BoomBoxRobotics/Anubis/Daughterboard/x5fusion.png

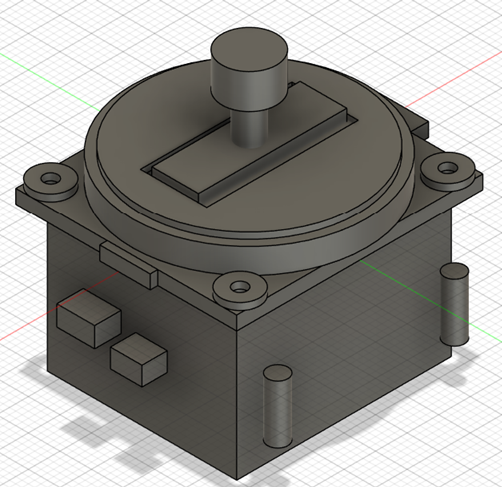
Daughterboard/x5fusion.png
