BoomBoxRobotics/Anubis/Daughterboard/fetoptions.bmp

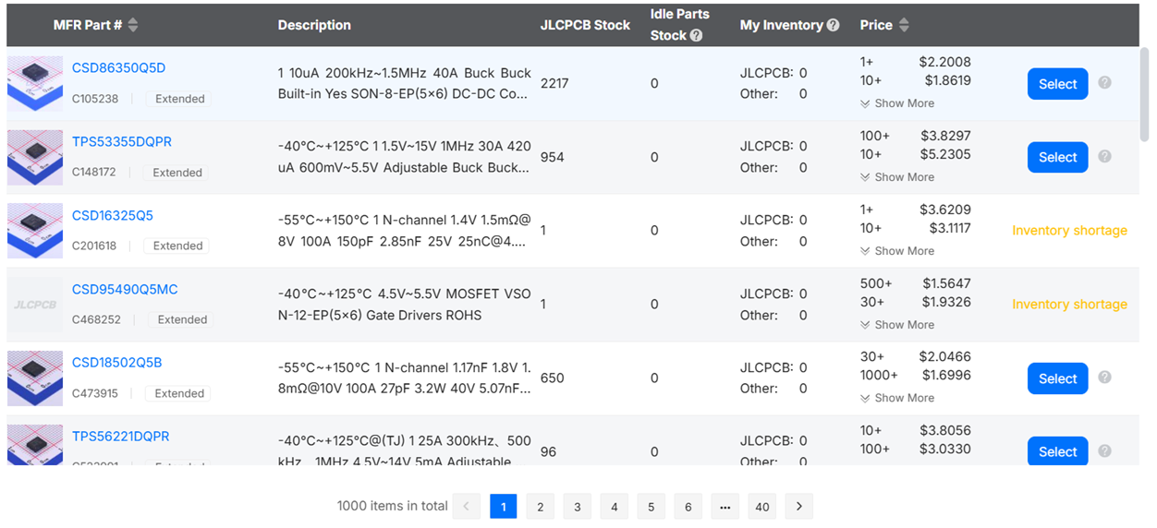
Daughterboard/fetoptions.bmp
