BoomBoxRobotics/Anubis/Daughterboard/U2.bmp

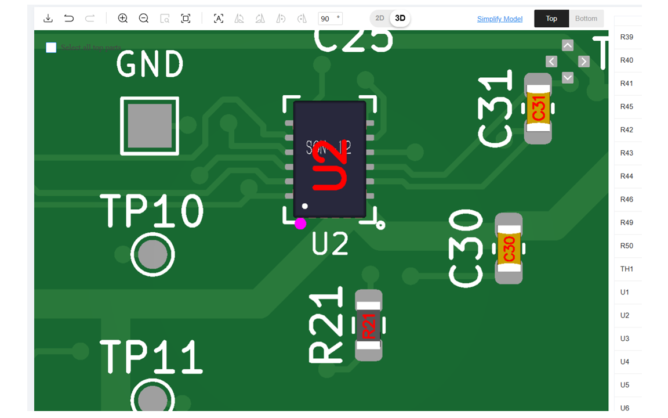
Daughterboard/U2.bmp
