BoomBoxRobotics/Anubis/Daughterboard/x5dimensions.webp

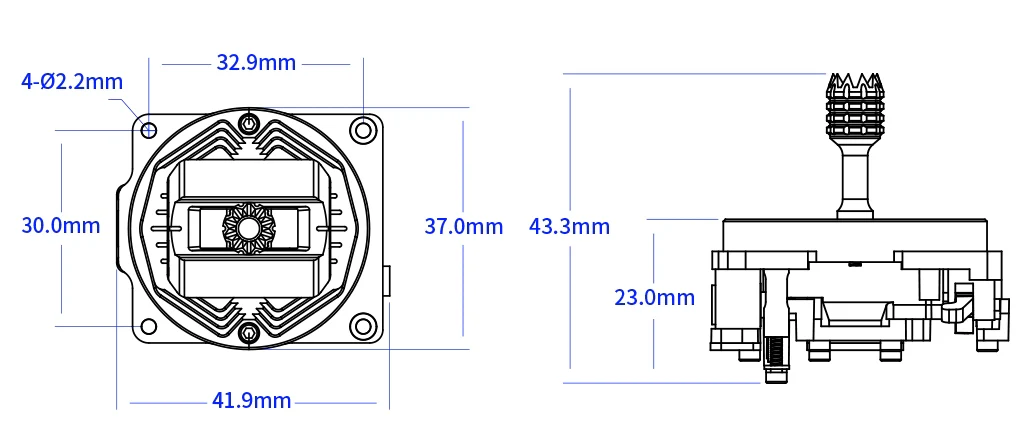
Daughterboard/x5dimensions.webp
