BoomBoxRobotics/Anubis/Daughterboard/x5Side1.webp

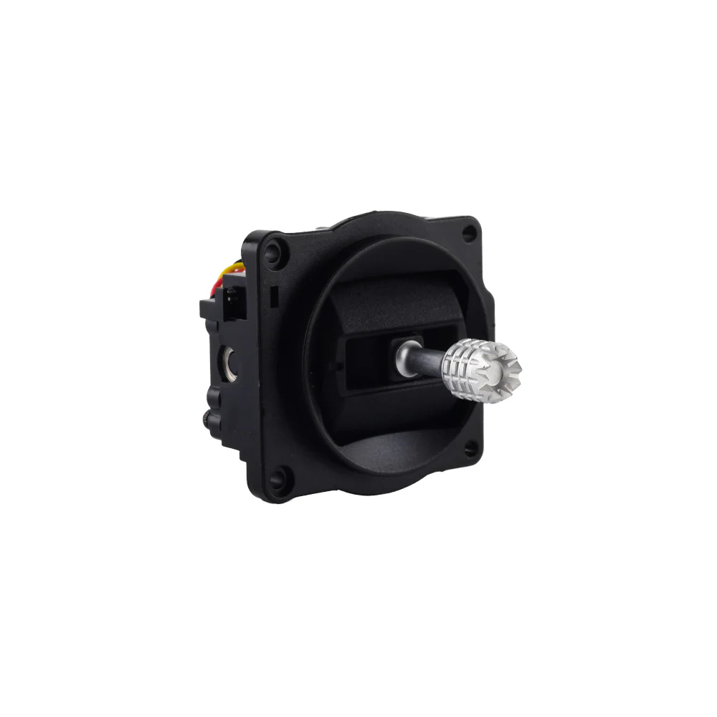
Daughterboard/x5Side1.webp
