BoomBoxRobotics/Anubis/Daughterboard/x5Side3.jpg

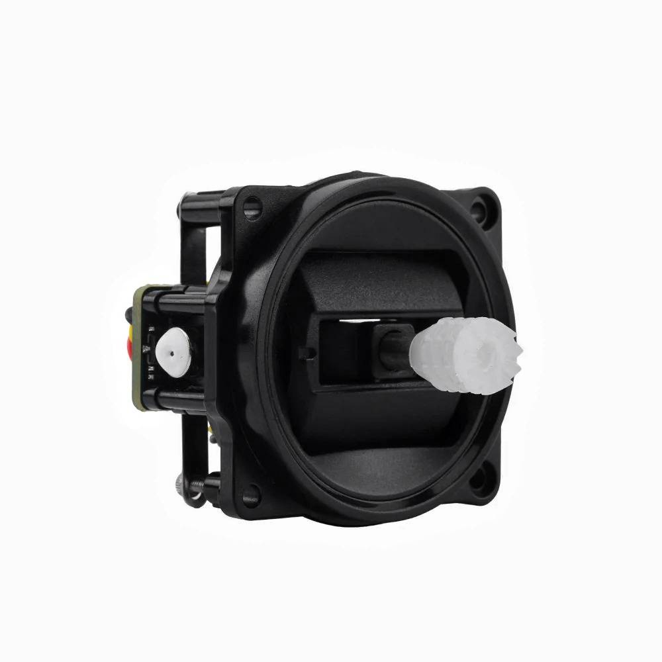
Daughterboard/x5Side3.jpg
