BoomBoxRobotics/Anubis/Hosyond_apr24b/Daughterboard/Daughterboard_pinlevel_preview.png

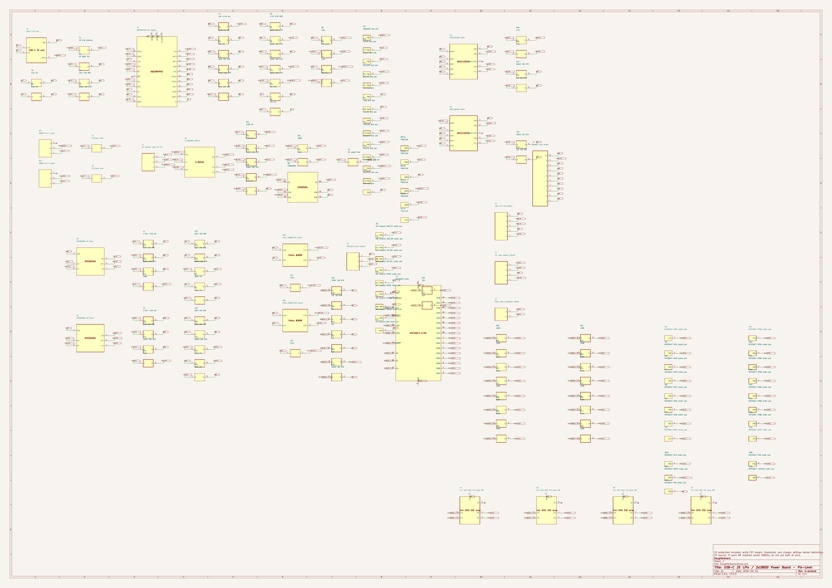
Hosyond_apr24b/Daughterboard/Daughterboard_pinlevel_preview.png
