BoomBoxRobotics/Anubis/Hosyond_apr24b/Games/Dungeon_Run_Pickups.png

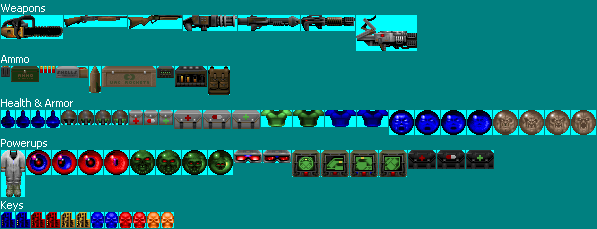
Hosyond_apr24b/Games/Dungeon_Run_Pickups.png
