BoomBoxRobotics/Anubis/Hosyond_apr24b/Games/Dungeon_Run_Text.png

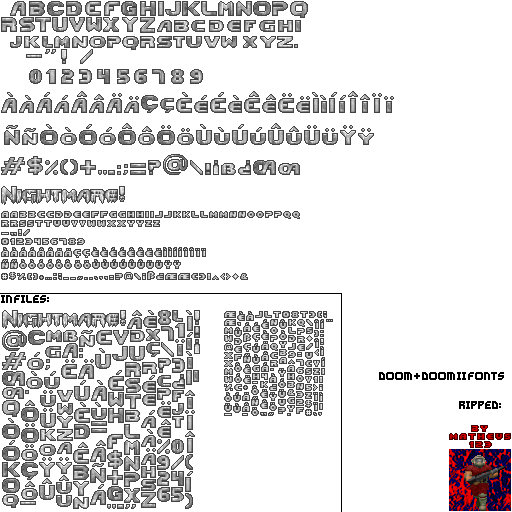
Hosyond_apr24b/Games/Dungeon_Run_Text.png
