BoomBoxRobotics/Anubis/Hosyond_apr24b/Games/Dungeon_Run_Weapons.png

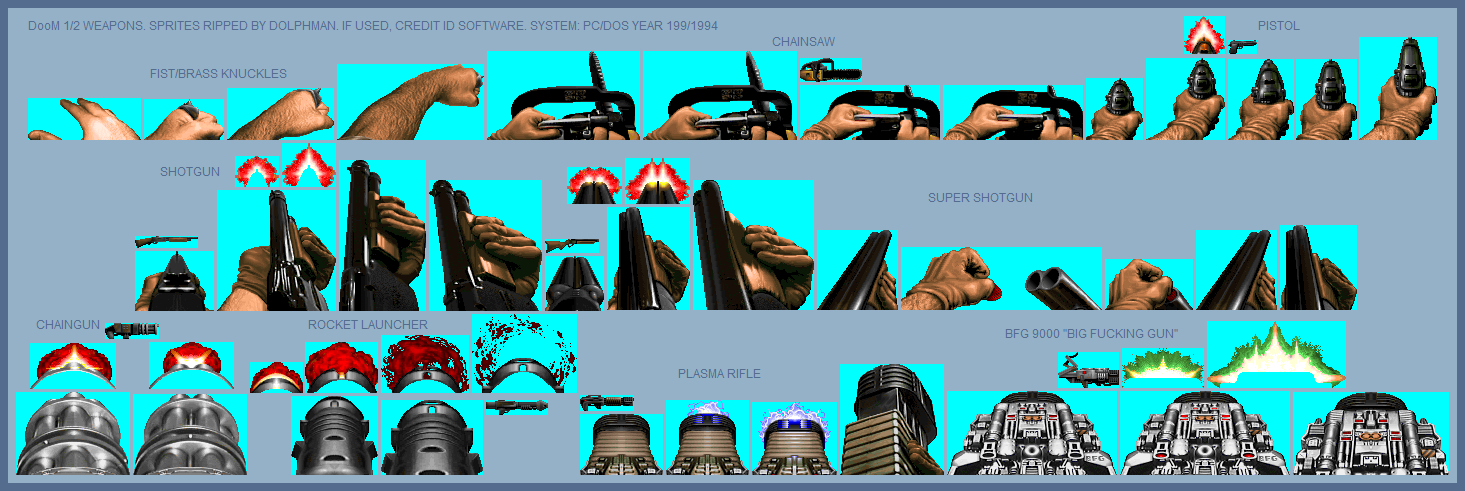
Hosyond_apr24b/Games/Dungeon_Run_Weapons.png
