BoomBoxRobotics/Anubis/Hosyond_apr24b/Daughterboard/Daughterboard_architecture_bom.csv

Refs | Value | Footprint | Qty | DNP
A1 | Fuse + VBUS TVS + CIN |  | 1
A2 | BQ2970 + dual NFET |  | 1
BT1 | 2x 18650 1S2P |  | 1
J1 | USB-C 5V Sink |  | 1
J2 | Power outputs |  | 1
J3 | Hosyond ESP32-S3 GPIO |  | 1
SW1 | Pololu #2808 5V switch |  | 1
SW2 | Pololu #2808 3V3 switch |  | 1
U1 | BQ24074RGT |  | 1
U3 | TPS61023 5V |  | 1
U4 | TPS63031 3V3 |  | 1
