BoomBoxRobotics/Anubis/Daughterboard/fabrication/jlcpcb_2026-07-14_r16/assembly/Daughterboard_jlcpcb_bom_template_filled_preview.png

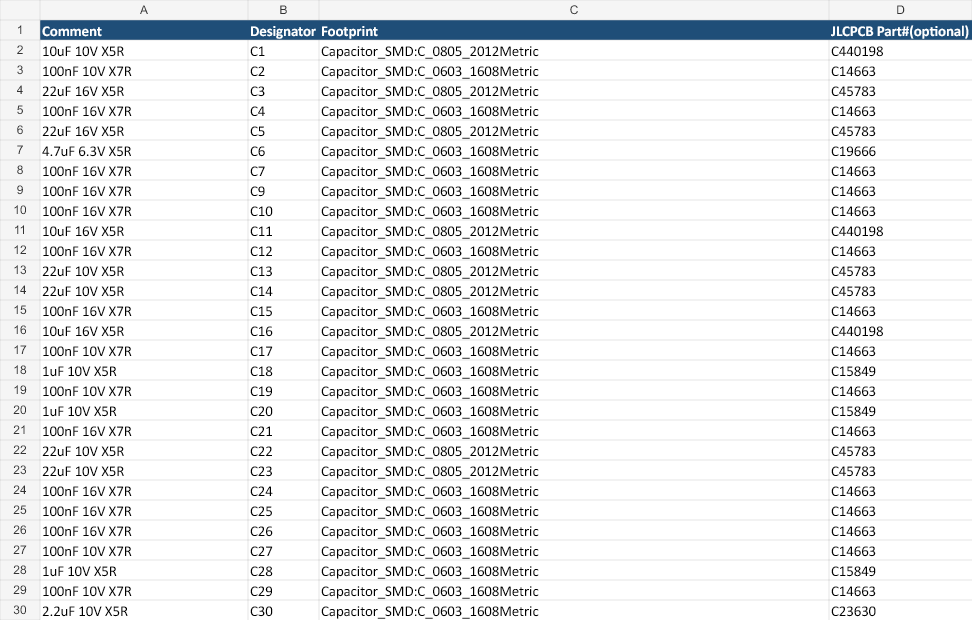
Daughterboard/fabrication/jlcpcb_2026-07-14_r16/assembly/Daughterboard_jlcpcb_bom_template_filled_preview.png
